UzixLS/mist1010-board/images/rev.A1.back.webp

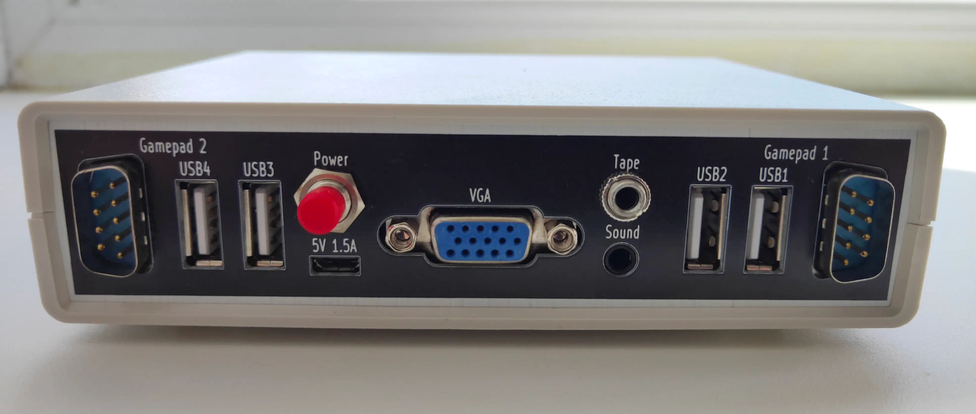
images/rev.A1.back.webp
